Feneck91/Pixelamp_Ext/pixelampext/src/animationtext.cpp

#include "../include/animationtext.h"
#include "../include/engine.h"

#ifdef SIMULATION
    #ifdef _DEBUG
        #include "../simu_include/TrackAllocation.h"
    #endif
#endif

//========================================================================
// 
//               All functions / structures for text sprites
// 
//========================================================================
/// <summary>
/// Structure that contains all sprites.
/// </summary>
struct tTextChar
{
    const char                  Character;
    const SpriteDefinitionPtr&  rSprite;
};

// Forward reference
const tTextChar* GetCharSpriteInfo(char _cChar);

//========================================================================
// 
//                       Class CAnimationText
// 
//========================================================================

CAnimationText::CAnimationText(String _strText, CRGB _crTextColor, bool _bMove, uint16_t _ui16Duration)
    : m_strText(_strText)
    , m_crTextColor(_crTextColor)
    , m_bMove(_bMove)
    , m_ui16Duration(_ui16Duration)
{
}

CAnimationText::~CAnimationText()
{
}

// Make the animation
bool CAnimationText::Loop()
{
    CEngine::Instance().ClearAllMatrix();
    bool bOnePixelBisible = (m_ui16Duration != 0); // false if m_ui16Duration is 0 / true (and so has no effect) if duration is set
    bool bQuitTheLoop     = false;

    // Display all sprites
    for (auto it = m_arrSpritesText.begin(); it != m_arrSpritesText.end(); ++it)
    {
        if ((*it)->ShowSprite(false, false, false))
        {
            bOnePixelBisible = true; // Don't quit animation IF at least one pixel is dîsplayed
        }
        if (m_bMove)
        {
            (*it)->MoveSprite(); // Move
        }
    }
    FastLED.show();

    if (m_ui16Duration != 0)
    {
        if (m_ui16Duration <= GetMillisecondWait())
        {   // Leave the animation
            m_ui16Duration = 0;
            bQuitTheLoop   = true;
        }
        else
        {   // Less time
            m_ui16Duration -= GetMillisecondWait();
        }
    }

    return !bOnePixelBisible || bQuitTheLoop;
}

void CAnimationText::Enter()
{
    // Call base class
    CAnimationBase::Enter();

    uint8_t ui8X    = 0;
    uint8_t uiWidth = 0;

    for (int iIndex = 0; iIndex < m_strText.length(); ++iIndex)
    {
        const tTextChar* pInfo = GetCharSpriteInfo(m_strText[iIndex]);
        if (pInfo != nullptr)
        {
            ColorReplacement cr;
            cr.AddColorReplacement(ColorReplacement::stColors{ 1, (uint32_t) m_crTextColor });
            m_arrSpritesText.push_back(pInfo->rSprite.ToSprite(cr));
            m_arrSpritesText.back()->m_X += ui8X;
            m_arrSpritesText.back()->m_Y += 1;
            ui8X += 1 + m_arrSpritesText.back()->m_ui8Width;
            m_arrSpritesText.back()->m_i8MxdX = -1;
            m_arrSpritesText.back()->m_i8MxdY = 0;
            uiWidth += 1 + m_arrSpritesText.back()->m_ui8Width;
        }
    }
    auto val = m_arrSpritesText.front()->m_X;
    if (!m_bMove)
    {
        uint8_t uiDeltaX = (uiWidth - 1) / 2 - 1;
        for (auto it = m_arrSpritesText.begin(); it != m_arrSpritesText.end(); ++it)
        {
            (*it)->MoveSprite(-uiDeltaX, 0); // Move X
        }
    }
}

void CAnimationText::Leave()
{
    // Call base class
    CAnimationBase::Leave();
    m_arrSpritesText.clear(); // No more need
}

uint16_t CAnimationText::GetMillisecondWait()
{
    return 125;
}

uint16_t CAnimationText::GetNumberAnimations()
{
    return 1;
}

void CAnimationText::SetCurrentAnimation(uint16_t _uiCurrentAnimation)
{
    CAnimationBase::SetCurrentAnimation(_uiCurrentAnimation);
}

//========================================================================
// 
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
    0, 1,
    1, 0,
    {
        1, 1, 1, 1,
        0, 0, 0, 1,
        0, 0, 1, 0,
        0, 1, 0, 0,
        1, 1, 1, 1,
    }
};

const SpriteDefinition<12> sprite_z PROGMEM
{
    3, 4,
    0, 2,
    1, 0,
    {
        1, 1, 1,
        0, 0, 1,
        0, 1, 0,
        1, 1, 1,
    }
};

const struct tTextChar g_AllText[] =
{
    {   '0', SpriteDefinitionPtrTemlate<20>(sprite_0)
    },
    {   '1', SpriteDefinitionPtrTemlate<15>(sprite_1)
    },
    {   '2', SpriteDefinitionPtrTemlate<20>(sprite_2)
    },
    {   '3', SpriteDefinitionPtrTemlate<20>(sprite_3)
    },
    {   '4', SpriteDefinitionPtrTemlate<20>(sprite_4)
    },
    {   '5', SpriteDefinitionPtrTemlate<20>(sprite_5)
    },
    {   '6', SpriteDefinitionPtrTemlate<20>(sprite_6)
    },
    {   '7', SpriteDefinitionPtrTemlate<20>(sprite_7)
    },
    {   '8', SpriteDefinitionPtrTemlate<20>(sprite_8)
    },
    {   '9', SpriteDefinitionPtrTemlate<20>(sprite_9)
    },
    {   'è', SpriteDefinitionPtrTemlate<18>(sprite_e_grave)
    },
    {   'é', SpriteDefinitionPtrTemlate<18>(sprite_e_aigu)
    },
    {   'ê', SpriteDefinitionPtrTemlate<18>(sprite_e_circon)
    },
    {   'A', SpriteDefinitionPtrTemlate<20>(sprite_A)
    },
    {   'a', SpriteDefinitionPtrTemlate<12>(sprite_a)
    },
    {   'B', SpriteDefinitionPtrTemlate<20>(sprite_B)
    },
    {   'b', SpriteDefinitionPtrTemlate<15>(sprite_b)
    },
    {   'C', SpriteDefinitionPtrTemlate<20>(sprite_C)
    },
    {   'c', SpriteDefinitionPtrTemlate<12>(sprite_c)
    },
    {   'D', SpriteDefinitionPtrTemlate<20>(sprite_D)
    },
    {   'd', SpriteDefinitionPtrTemlate<15>(sprite_d)
    },
    {   'E', SpriteDefinitionPtrTemlate<20>(sprite_E)
    },
    {   'e', SpriteDefinitionPtrTemlate<12>(sprite_e)
    },
    {   'F', SpriteDefinitionPtrTemlate<20>(sprite_F)
    },
    {   'f', SpriteDefinitionPtrTemlate<15>(sprite_f)
    },
    {   'G', SpriteDefinitionPtrTemlate<20>(sprite_G)
    },
    {   'g', SpriteDefinitionPtrTemlate<15>(sprite_g)
    },
    {   'H', SpriteDefinitionPtrTemlate<20>(sprite_H)
    },
    {   'h', SpriteDefinitionPtrTemlate<15>(sprite_h)
    },
    {   'I', SpriteDefinitionPtrTemlate<5>(sprite_I)
    },
    {   'i', SpriteDefinitionPtrTemlate<5>(sprite_i)
    },
    {   'J', SpriteDefinitionPtrTemlate<20>(sprite_J)
    },
    {   'j', SpriteDefinitionPtrTemlate<10>(sprite_j)
    },
    {   'K', SpriteDefinitionPtrTemlate<20>(sprite_K)
    },
    {   'k', SpriteDefinitionPtrTemlate<15>(sprite_k)
    },
    {   'L', SpriteDefinitionPtrTemlate<15>(sprite_L)
    },
    {   'l', SpriteDefinitionPtrTemlate<10>(sprite_l)
    },
    {   'M', SpriteDefinitionPtrTemlate<25>(sprite_M)
    },
    {   'm', SpriteDefinitionPtrTemlate<20>(sprite_m)
    },
    {   'N', SpriteDefinitionPtrTemlate<20>(sprite_N)
    },
    {   'n', SpriteDefinitionPtrTemlate<16>(sprite_n)
    },
    {   'O', SpriteDefinitionPtrTemlate<20>(sprite_O)
    },
    {   'o', SpriteDefinitionPtrTemlate<16>(sprite_o)
    },
    {   'P', SpriteDefinitionPtrTemlate<20>(sprite_P)
    },
    {   'p', SpriteDefinitionPtrTemlate<12>(sprite_p)
    },
    {   'Q', SpriteDefinitionPtrTemlate<20>(sprite_Q)
    },
    {   'q', SpriteDefinitionPtrTemlate<12>(sprite_q)
    },
    {   'R', SpriteDefinitionPtrTemlate<20>(sprite_R)
    },
    {   'r', SpriteDefinitionPtrTemlate<12>(sprite_r)
    },
    {   'S', SpriteDefinitionPtrTemlate<20>(sprite_S)
    },
    {   's', SpriteDefinitionPtrTemlate<12>(sprite_s)
    },
    {   'T', SpriteDefinitionPtrTemlate<15>(sprite_T)
    },
    {   't', SpriteDefinitionPtrTemlate<15>(sprite_t)
    },
    {   'U', SpriteDefinitionPtrTemlate<20>(sprite_U)
    },
    {   'u', SpriteDefinitionPtrTemlate<12>(sprite_u)
    },
    {   'V', SpriteDefinitionPtrTemlate<15>(sprite_V)
    },
    {   'v', SpriteDefinitionPtrTemlate<12>(sprite_v)
    },
    {   'W', SpriteDefinitionPtrTemlate<25>(sprite_W)
    },
    {   'w', SpriteDefinitionPtrTemlate<20>(sprite_w)
    },
    {   'X', SpriteDefinitionPtrTemlate<15>(sprite_X)
    },
    {   'x', SpriteDefinitionPtrTemlate<12>(sprite_x)
    },
    {   'Y', SpriteDefinitionPtrTemlate<15>(sprite_Y)
    },
    {   'y', SpriteDefinitionPtrTemlate<12>(sprite_y)
    },
    {   'Z', SpriteDefinitionPtrTemlate<20>(sprite_Z)
    },
    {   'z', SpriteDefinitionPtrTemlate<12>(sprite_z)
    },
};

/// <summary>
/// Get the sprite info.
/// 
/// Not very fast but it don't take too much memory.
/// </summary>
/// <param name="_cChar">Char to find.</param>
/// <returns>The sprite info if found, nullptr if not found.</returns>
const tTextChar* GetCharSpriteInfo(char _cChar)
{
    const tTextChar* pTextCharRet = nullptr;
    for (int iIndex = 0; iIndex < sizeof(g_AllText) / sizeof(g_AllText[0]); ++iIndex)
    {
        if (g_AllText[iIndex].Character == _cChar)
        {
            pTextCharRet = &g_AllText[iIndex];
            break;
        }
    }

    return pTextCharRet;
}
